tortellini13/Acoustic-Camera/Captures/image_20250306160753.png

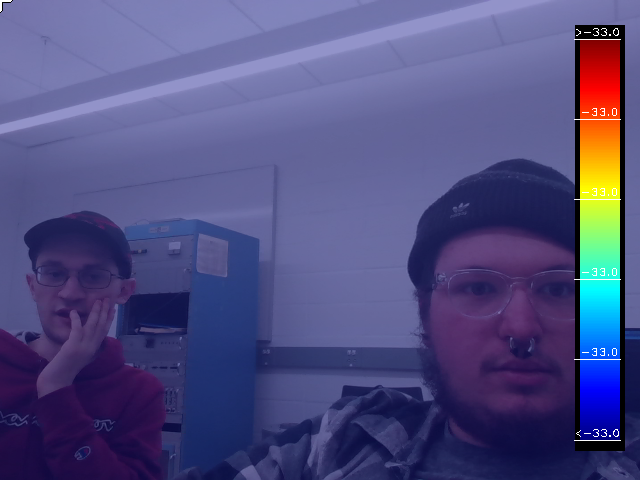
Captures/image_20250306160753.png
