tortellini13/Acoustic-Camera/Captures/image_20250403122320.png

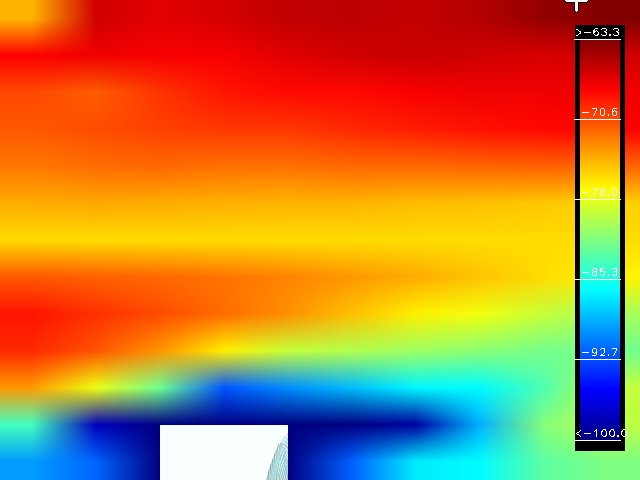
Captures/image_20250403122320.png
