tortellini13/Acoustic-Camera/Captures/image_20250403122324.png

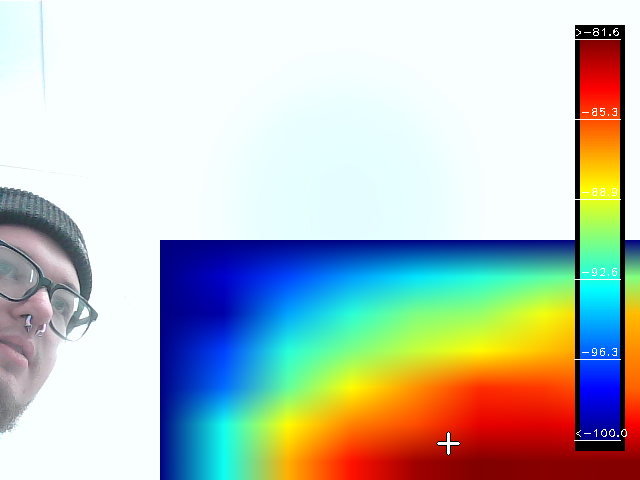
Captures/image_20250403122324.png
