tortellini13/Acoustic-Camera/Captures/image_20250403122325.png

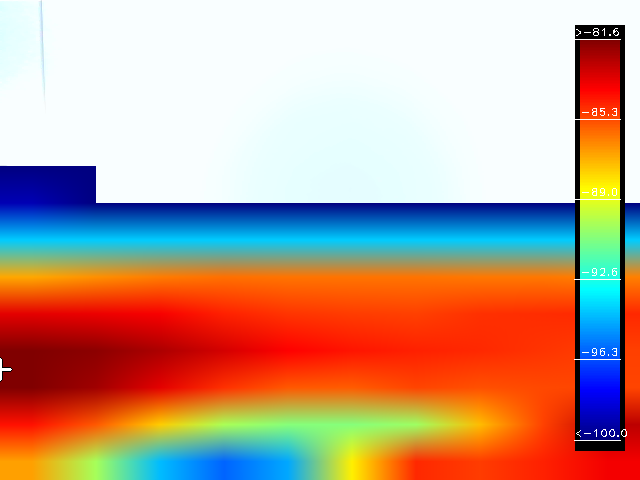
Captures/image_20250403122325.png
