tortellini13/Acoustic-Camera/Captures/image_20250407164208.png

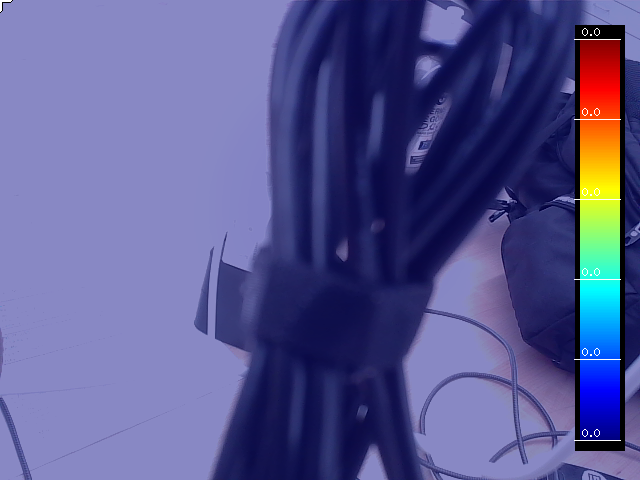
Captures/image_20250407164208.png
