tortellini13/Acoustic-Camera/Captures/image_20250407164211.png

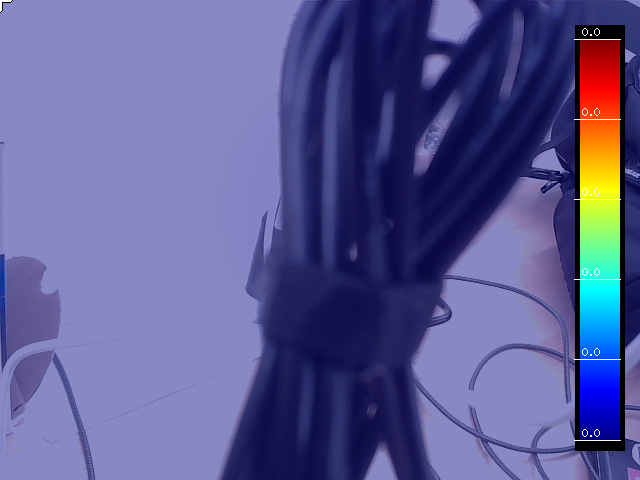
Captures/image_20250407164211.png
