tortellini13/Acoustic-Camera/Captures/image_20250407164213.png

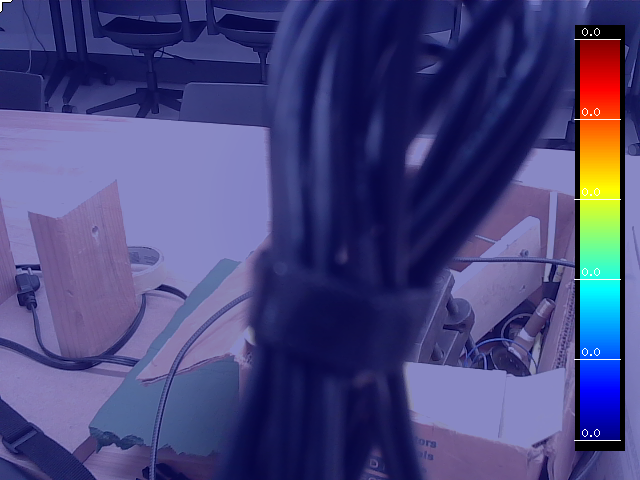
Captures/image_20250407164213.png
