tortellini13/Acoustic-Camera/Captures/image_20250407164214.png

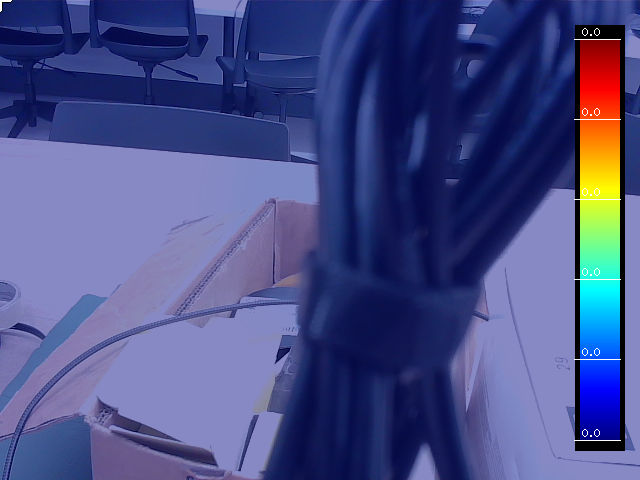
Captures/image_20250407164214.png
