tortellini13/Acoustic-Camera/Depricated/main-PhasednewSrtuct.cpp

#include <opencv2/opencv.hpp>
#include <iostream>
#include <vector>
#include <ctime>
#include <chrono>
#include <iomanip>

#include "PARAMS.h"
#include "ALSA.h"
#include "Beamform.h"
#include "Video.h"
#include "Timer.h"

using namespace std;
using namespace cv;

//==============================================================================================

int main() 
{
    /*
    - Initialize video class
    - initializeWindow
    - Start while loop
    - cap >> frame
    - perform all frame functions
    - imshow(result from frame functions)
    - Break if close key is pressed
    - ~video() after while loop
    */

    double max_frame_time = 1 / (static_cast<double>(SAMPLE_RATE) / static_cast<double>(FFT_SIZE));
    
    //==============================================================================================
    
    // Video frame and capture settings
    // Set framerate of capture from PARAMS.h
    int codec = VideoWriter::fourcc('M', 'J', 'P', 'G'); // Set codec of video recording
    string video_file_name = "testoutput";           // Set video file output file name
    
    // Audio data [M * N * FFT_SIZE]
    //float audio_data[NUM_CHANNELS * FFT_SIZE] = {0.0f};
    array3D<float> audio_data(M_AMOUNT, N_AMOUNT, FFT_SIZE);

    // Beamformed and post-processed data [NUM_ANGLES * NUMANGLES]
    //float processed_data[TOTAL_ANGLES] = {0.0f};
    Mat processed_data(NUM_ANGLES, NUM_ANGLES, CV_32FC1, Scalar(0));

    // Output from all video processing to show
    Mat frame;
    
    // Initialize classes
    ALSA ALSA(AUDIO_DEVICE_NAME, NUM_CHANNELS, SAMPLE_RATE, FFT_SIZE);
    beamform beamform(FFT_SIZE, SAMPLE_RATE, M_AMOUNT, N_AMOUNT, MIC_SPACING, NUM_ANGLES, MIN_ANGLE, MAX_ANGLE, ANGLE_STEP);
    video video(RESOLUTION_WIDTH, RESOLUTION_HEIGHT, FRAME_RATE);

    //==============================================================================================

    // Create timers for debugging
    timer video_time("Video");
    timer ALSA_time("ALSA");
    timer beamform_time("Beamform");

    //==============================================================================================
    
    // Setup audio and data processing
    ALSA.setup();

    beamform.setup(audio_data);

    //video.initializeWindow();

    // Open window
    video.startCapture();

    cout << "Starting loop.\n";
    // Loop to calculate audio and display video
    while (1)
    {
        #ifdef PROFILE_MAIN
        ALSA_time.start();
        #endif

        // Recieve audio and process data
        ALSA.recordAudio(audio_data);
        //cout << "recordAudio.\n"; // (debugging)

        #ifdef PRINT_AUDIO
        // Print out first frame of audio data
        for (int n = 0; n < N_AMOUNT; n++)
        {
            for (int m = 0; m < M_AMOUNT; m++)
            {
                float sum = 0;
                for (int b = 0; b < FFT_SIZE; b++)
                {
                    sum = audio_data.at(m, n, b);
                }
                cout << setw(8) << fixed << setprecision(6) << showpos << sum * 100.0f << " ";
            }
            cout << endl;
        }
        cout << endl;
        #endif
        #ifdef PROFILE_MAIN
        ALSA_time.end();

        beamform_time.start();
        #endif
        beamform.processData(audio_data, processed_data, 16, 24, POST_dBFS); // 1kHz Full Octave Band
        //cout << "processData.\n"; // (debugging)
        
        #ifdef PROFILE_MAIN
        beamform_time.end();

        video_time.start();
        #endif
        // Does all processing to frame including drawing UI and doing heat map
        video.processFrame(processed_data, -70.0f, -30.0f);
       
        #ifdef PROFILE_MAIN
        video_time.end();

        //==============================================================================================

        double total_time = ALSA_time.time() + beamform_time.time() + video_time.time();
        
        ALSA_time.print();
        beamform_time.print();
        video_time.print();
        cout << "Total time: " << total_time << " seconds.\n\n";
        #endif

        // Break loop if any key is pressed
        if (waitKey(1) >= 0) break;
    
    } // end loop
    video.stopCapture();

    return 0;
} // end main
